KubbyDev/hen-translator/Software/Tests/Speaker/Speaker.ino

/* "He's A Pirate" / "Pirates of the Caribbean" Theme Song Playing
 * By Xitang 2016.06.27 
 * Youtube in Action: https://youtu.be/sjPAj1lXgtk
 * 
 * INSTRUCTION: Hook up Pin 10 to the positive side of a buzzer or a microphone, hook up 
 * any resistor to the negative side of a buzzer (to limit current & volume & to protect the pin), 
 * and then connect the other end of the resistor to ground pin. Upload the sketch and enjoy! 
 * 
 * Music notes of the song obtained from Easy Music (Great website)
 * Link: http://easymusic.altervista.org/recorder-hes-a-pirate-pirates-of-caribbean-sheet-music-guitar-chords/
 * 
 * Also would like to credit Musicnotes's "How to Read Sheet Music" Guide
 * Link: http://www.musicnotes.com/blog/2014/04/11/how-to-read-sheet-music/
 * 
 * Code inspired by Chapter 5 of Jeremy Blum's book "Exploring Arduino"
 * Link: http://www.exploringarduino.com/content/ch5/
 * 
 * Music notes' frequencies obtained from arduino website
 * Link: https://www.arduino.cc/en/Tutorial/toneMelody
 */

#define BUZZER 9

const float songspeed = 1.5;

#define NOTE_C4  262
#define NOTE_D4  294
#define NOTE_E4  330
#define NOTE_F4  349
#define NOTE_G4  392
#define NOTE_A4  440
#define NOTE_B4  494
#define NOTE_C5  523
#define NOTE_D5  587
#define NOTE_E5  659
#define NOTE_F5  698
#define NOTE_G5  784
#define NOTE_A5  880
#define NOTE_B5  988

int notes[] = {
   NOTE_E4, NOTE_G4, NOTE_A4, NOTE_A4, 0, 
   NOTE_A4, NOTE_B4, NOTE_C5, NOTE_C5, 0, 
   NOTE_C5, NOTE_D5, NOTE_B4, NOTE_B4, 0,
   NOTE_A4, NOTE_G4, NOTE_A4, 0,
   
   NOTE_E4, NOTE_G4, NOTE_A4, NOTE_A4, 0, 
   NOTE_A4, NOTE_B4, NOTE_C5, NOTE_C5, 0, 
   NOTE_C5, NOTE_D5, NOTE_B4, NOTE_B4, 0,
   NOTE_A4, NOTE_G4, NOTE_A4, 0,
   
   NOTE_E4, NOTE_G4, NOTE_A4, NOTE_A4, 0, 
   NOTE_A4, NOTE_C5, NOTE_D5, NOTE_D5, 0, 
   NOTE_D5, NOTE_E5, NOTE_F5, NOTE_F5, 0,
   NOTE_E5, NOTE_D5, NOTE_E5, NOTE_A4, 0,
   
   NOTE_A4, NOTE_B4, NOTE_C5, NOTE_C5, 0, 
   NOTE_D5, NOTE_E5, NOTE_A4, 0, 
   NOTE_A4, NOTE_C5, NOTE_B4, NOTE_B4, 0,
   NOTE_C5, NOTE_A4, NOTE_B4, 0,

   NOTE_A4, NOTE_A4, 
   //Repeat of first part
   NOTE_A4, NOTE_B4, NOTE_C5, NOTE_C5, 0, 
   NOTE_C5, NOTE_D5, NOTE_B4, NOTE_B4, 0,
   NOTE_A4, NOTE_G4, NOTE_A4, 0,

   NOTE_E4, NOTE_G4, NOTE_A4, NOTE_A4, 0, 
   NOTE_A4, NOTE_B4, NOTE_C5, NOTE_C5, 0, 
   NOTE_C5, NOTE_D5, NOTE_B4, NOTE_B4, 0,
   NOTE_A4, NOTE_G4, NOTE_A4, 0,
   
   NOTE_E4, NOTE_G4, NOTE_A4, NOTE_A4, 0, 
   NOTE_A4, NOTE_C5, NOTE_D5, NOTE_D5, 0, 
   NOTE_D5, NOTE_E5, NOTE_F5, NOTE_F5, 0,
   NOTE_E5, NOTE_D5, NOTE_E5, NOTE_A4, 0,
   
   NOTE_A4, NOTE_B4, NOTE_C5, NOTE_C5, 0, 
   NOTE_D5, NOTE_E5, NOTE_A4, 0, 
   NOTE_A4, NOTE_C5, NOTE_B4, NOTE_B4, 0,
   NOTE_C5, NOTE_A4, NOTE_B4, 0,
   //End of Repeat

   NOTE_E5, 0, 0, NOTE_F5, 0, 0,
   NOTE_E5, NOTE_E5, 0, NOTE_G5, 0, NOTE_E5, NOTE_D5, 0, 0,
   NOTE_D5, 0, 0, NOTE_C5, 0, 0,
   NOTE_B4, NOTE_C5, 0, NOTE_B4, 0, NOTE_A4,

   NOTE_E5, 0, 0, NOTE_F5, 0, 0,
   NOTE_E5, NOTE_E5, 0, NOTE_G5, 0, NOTE_E5, NOTE_D5, 0, 0,
   NOTE_D5, 0, 0, NOTE_C5, 0, 0,
   NOTE_B4, NOTE_C5, 0, NOTE_B4, 0, NOTE_A4
};

int duration[] = {
  125, 125, 250, 125, 125, 
  125, 125, 250, 125, 125,
  125, 125, 250, 125, 125,
  125, 125, 375, 125, 
  
  125, 125, 250, 125, 125, 
  125, 125, 250, 125, 125,
  125, 125, 250, 125, 125,
  125, 125, 375, 125, 
  
  125, 125, 250, 125, 125, 
  125, 125, 250, 125, 125,
  125, 125, 250, 125, 125,
  125, 125, 125, 250, 125,

  125, 125, 250, 125, 125, 
  250, 125, 250, 125, 
  125, 125, 250, 125, 125,
  125, 125, 375, 375,

  250, 125,
  //Rpeat of First Part
  125, 125, 250, 125, 125,
  125, 125, 250, 125, 125,
  125, 125, 375, 125, 
  
  125, 125, 250, 125, 125, 
  125, 125, 250, 125, 125,
  125, 125, 250, 125, 125,
  125, 125, 375, 125, 
  
  125, 125, 250, 125, 125, 
  125, 125, 250, 125, 125,
  125, 125, 250, 125, 125,
  125, 125, 125, 250, 125,

  125, 125, 250, 125, 125, 
  250, 125, 250, 125, 
  125, 125, 250, 125, 125,
  125, 125, 375, 375,
  //End of Repeat
  
  250, 125, 375, 250, 125, 375,
  125, 125, 125, 125, 125, 125, 125, 125, 375,
  250, 125, 375, 250, 125, 375,
  125, 125, 125, 125, 125, 500,

  250, 125, 375, 250, 125, 375,
  125, 125, 125, 125, 125, 125, 125, 125, 375,
  250, 125, 375, 250, 125, 375,
  125, 125, 125, 125, 125, 500
};

void setup() {

  Serial.begin(115200);
  while(!Serial);
  Serial.println("Starting song");
  
  for (int i = 0; i < sizeof(duration)/sizeof(int); i++) {
    int wait = duration[i] * songspeed;
    tone(BUZZER, notes[i], wait);
    delay(wait);
  }

  Serial.println("Song done");
}

void loop() {
}
